InaSusnoschi/trainAwear-app-v1/docs/html/classcom_1_1example_1_1trainawearapplication_1_1_biceps__inherit__graph.png

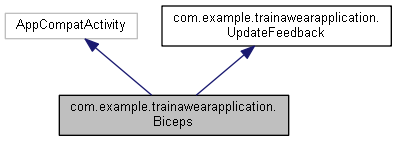
docs/html/classcom_1_1example_1_1trainawearapplication_1_1_biceps__inherit__graph.png
