InaSusnoschi/trainAwear-app-v1/docs/html/classcom_1_1example_1_1trainawearapplication_1_1_udp_client_handler__coll__graph.png

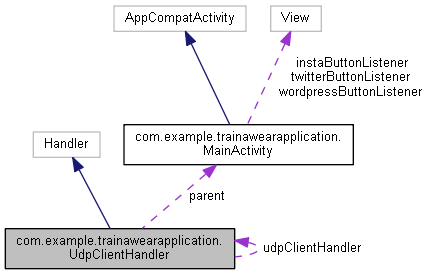
docs/html/classcom_1_1example_1_1trainawearapplication_1_1_udp_client_handler__coll__graph.png
