InaSusnoschi/trainAwear-app-v1/docs/html/inherit_graph_1.png

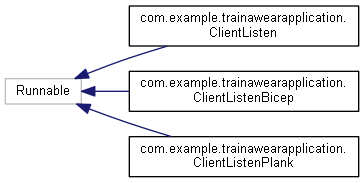
docs/html/inherit_graph_1.png
