InaSusnoschi/trainAwear-app-v1/docs/html/inherit_graph_7.png

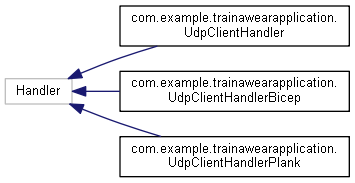
docs/html/inherit_graph_7.png
