InaSusnoschi/trainAwear-app-v1/docs/html/inherit_graph_8.png

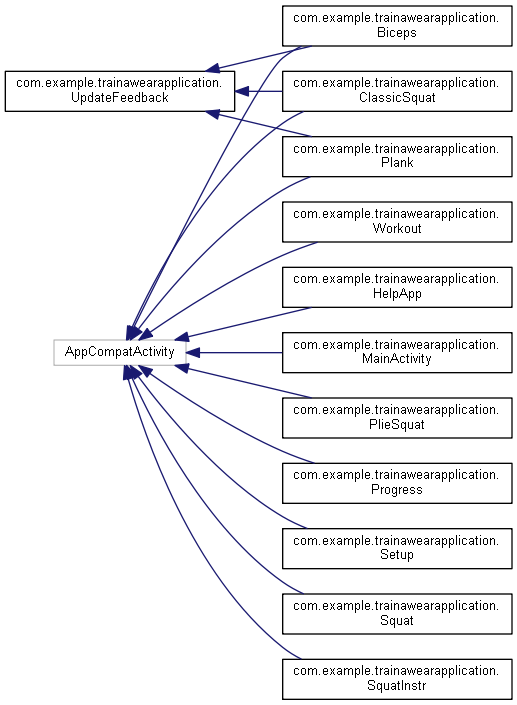
docs/html/inherit_graph_8.png
